nbalagopal/microsd-switch/board-pics/microsd-inaction/photo1.jpg

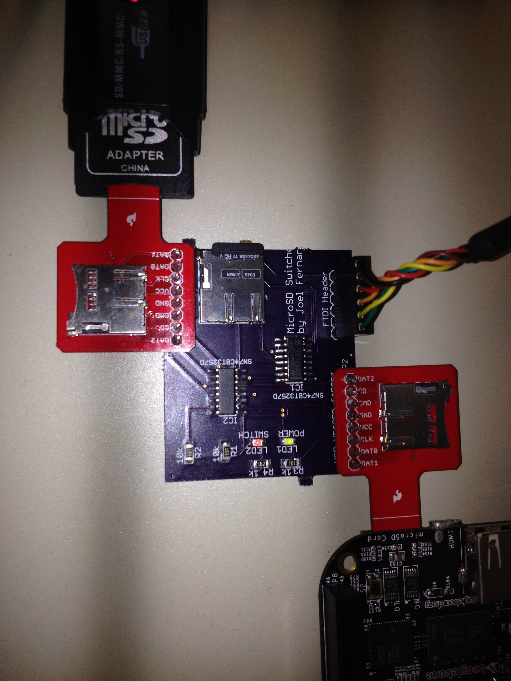
board-pics/microsd-inaction/photo1.jpg
