nbalagopal/microsd-switch/board-pics/microsd-inaction/photo2.jpg

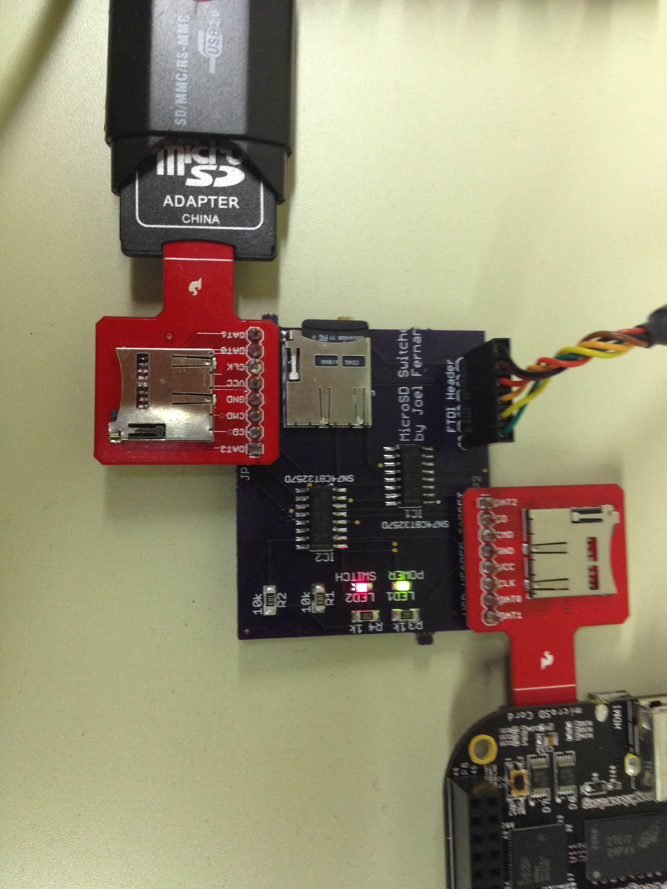
board-pics/microsd-inaction/photo2.jpg
