nbalagopal/microsd-switch/board-pics/microsd-inaction/photo3.jpg

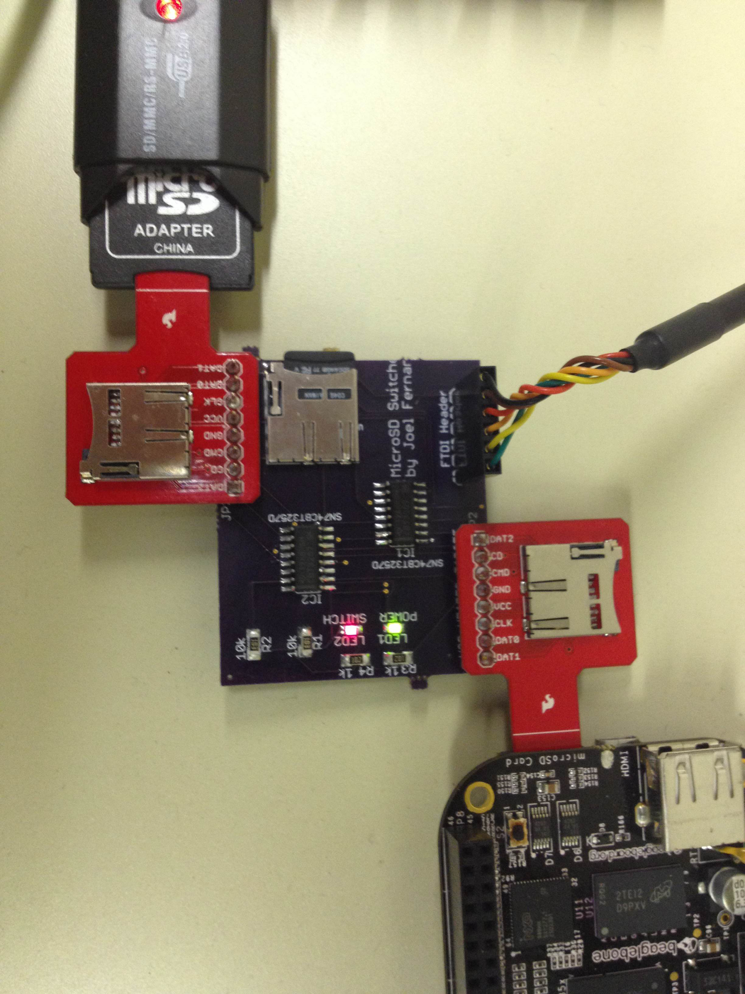
board-pics/microsd-inaction/photo3.jpg
