nbalagopal/microsd-switch/board-pics/microsd-inaction/photo6.jpg

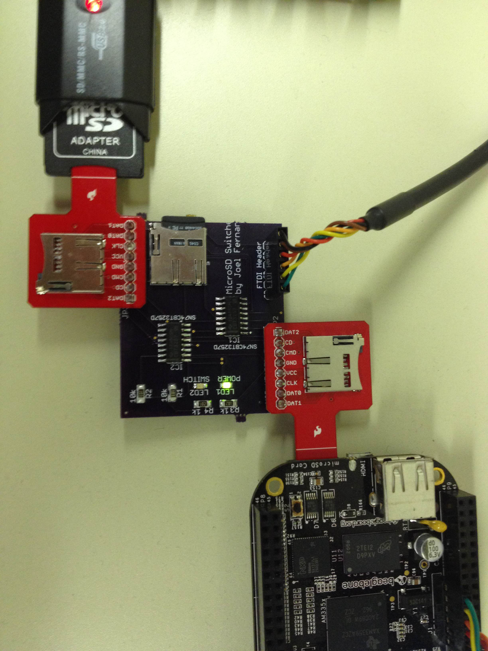
board-pics/microsd-inaction/photo6.jpg
